gabesk/xmascard/hdl/test_individual_leds.v

`timescale 1ns / 1ps

//
// Validates that updating a pattern works according to design.
//


// In testing on the hardware, PuTTY was having trouble reliably sending and
// receiving the lowercase letter 'a'. Nothing else; the test data here worked
// fine. So this variation attempts to figure out why.
// Wait a random amount of time, then send 'a', repeatedly over and over. If the
// receiver ever receives something other than 'a' back, assert.

module test;

    // Inputs
    reg clk = 0;
    reg rx = 1; // RS-232 idle condition is logic high
    reg xmit = 0;
    reg recv = 0;
    reg write_complete_received = 0;
    reg test_step_complete = 0;

    integer i = 0;
    integer j = 0;
    integer random_delay;
    reg [7:0] received_byte = 0;

    reg [7:0] test_send_vector [0:576];
    integer test_send_vector_len = 576;
    reg [7:0] test_receive_vector [0:384];
    integer test_receive_vector_len = 384;
    
    initial begin
        test_send_vector[0]  = "i";
        test_send_vector[1]  = 8'h0;
        test_send_vector[2]  = 8'h0;
        test_send_vector[3]  = "i";
        test_send_vector[4]  = 8'h0;
        test_send_vector[5]  = 8'h1;
        test_send_vector[6]  = "i";
        test_send_vector[7]  = 8'h0;
        test_send_vector[8]  = 8'h2;
        test_send_vector[9]  = "i";
        test_send_vector[10]  = 8'h0;
        test_send_vector[11]  = 8'h3;
        test_send_vector[12]  = "i";
        test_send_vector[13]  = 8'h0;
        test_send_vector[14]  = 8'h4;
        test_send_vector[15]  = "i";
        test_send_vector[16]  = 8'h0;
        test_send_vector[17]  = 8'h5;
        test_send_vector[18]  = "i";
        test_send_vector[19]  = 8'h0;
        test_send_vector[20]  = 8'h6;
        test_send_vector[21]  = "i";
        test_send_vector[22]  = 8'h0;
        test_send_vector[23]  = 8'h7;
        test_send_vector[24]  = "i";
        test_send_vector[25]  = 8'h1;
        test_send_vector[26]  = 8'h0;
        test_send_vector[27]  = "i";
        test_send_vector[28]  = 8'h1;
        test_send_vector[29]  = 8'h1;
        test_send_vector[30]  = "i";
        test_send_vector[31]  = 8'h1;
        test_send_vector[32]  = 8'h2;
        test_send_vector[33]  = "i";
        test_send_vector[34]  = 8'h1;
        test_send_vector[35]  = 8'h3;
        test_send_vector[36]  = "i";
        test_send_vector[37]  = 8'h1;
        test_send_vector[38]  = 8'h4;
        test_send_vector[39]  = "i";
        test_send_vector[40]  = 8'h1;
        test_send_vector[41]  = 8'h5;
        test_send_vector[42]  = "i";
        test_send_vector[43]  = 8'h1;
        test_send_vector[44]  = 8'h6;
        test_send_vector[45]  = "i";
        test_send_vector[46]  = 8'h1;
        test_send_vector[47]  = 8'h7;
        test_send_vector[48]  = "i";
        test_send_vector[49]  = 8'h2;
        test_send_vector[50]  = 8'h0;
        test_send_vector[51]  = "i";
        test_send_vector[52]  = 8'h2;
        test_send_vector[53]  = 8'h1;
        test_send_vector[54]  = "i";
        test_send_vector[55]  = 8'h2;
        test_send_vector[56]  = 8'h2;
        test_send_vector[57]  = "i";
        test_send_vector[58]  = 8'h2;
        test_send_vector[59]  = 8'h3;
        test_send_vector[60]  = "i";
        test_send_vector[61]  = 8'h2;
        test_send_vector[62]  = 8'h4;
        test_send_vector[63]  = "i";
        test_send_vector[64]  = 8'h2;
        test_send_vector[65]  = 8'h5;
        test_send_vector[66]  = "i";
        test_send_vector[67]  = 8'h2;
        test_send_vector[68]  = 8'h6;
        test_send_vector[69]  = "i";
        test_send_vector[70]  = 8'h2;
        test_send_vector[71]  = 8'h7;
        test_send_vector[72]  = "i";
        test_send_vector[73]  = 8'h3;
        test_send_vector[74]  = 8'h0;
        test_send_vector[75]  = "i";
        test_send_vector[76]  = 8'h3;
        test_send_vector[77]  = 8'h1;
        test_send_vector[78]  = "i";
        test_send_vector[79]  = 8'h3;
        test_send_vector[80]  = 8'h2;
        test_send_vector[81]  = "i";
        test_send_vector[82]  = 8'h3;
        test_send_vector[83]  = 8'h3;
        test_send_vector[84]  = "i";
        test_send_vector[85]  = 8'h3;
        test_send_vector[86]  = 8'h4;
        test_send_vector[87]  = "i";
        test_send_vector[88]  = 8'h3;
        test_send_vector[89]  = 8'h5;
        test_send_vector[90]  = "i";
        test_send_vector[91]  = 8'h3;
        test_send_vector[92]  = 8'h6;
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
        test_receive_vector[364]  = 8'h16;
        test_receive_vector[365]  = 8'h6;
        test_receive_vector[366]  = 8'h16;
        test_receive_vector[367]  = 8'h7;
        test_receive_vector[368]  = 8'h17;
        test_receive_vector[369]  = 8'h0;
        test_receive_vector[370]  = 8'h17;
        test_receive_vector[371]  = 8'h1;
        test_receive_vector[372]  = 8'h17;
        test_receive_vector[373]  = 8'h2;
        test_receive_vector[374]  = 8'h17;
        test_receive_vector[375]  = 8'h3;
        test_receive_vector[376]  = 8'h17;
        test_receive_vector[377]  = 8'h4;
        test_receive_vector[378]  = 8'h17;
        test_receive_vector[379]  = 8'h5;
        test_receive_vector[380]  = 8'h17;
        test_receive_vector[381]  = 8'h6;
        test_receive_vector[382]  = 8'h17;
        test_receive_vector[383]  = 8'h7;
    end
    // Outputs
    wire tx;
    wire [23:0] leds;

    // Instantiate the Unit Under Test (UUT)
    lights uut (
        .clk(clk),
        .rx(rx),
        .tx(tx),
        .leds(leds)
    );

    always #20 clk = ~clk;

    // Transmission loop
    initial begin
        // Wait 100 ns for global reset to finish and a little longer for good measure.
        #100;
        #1234;

        for (i=0; i<test_send_vector_len; i=i+1) begin
            $display("Send i: %d val: %x", i, test_send_vector[i]);
            xmit_byte(test_send_vector[i]);
            if ((i+1) % 3 == 0) @ (test_step_complete) test_step_complete = 0; // Wait for module to echo result back to us
            // Wait random time
            random_delay = $random % 1000000; // Up to 1 ms
            #(random_delay);
        end

        #1000000
        if (write_complete_received == 0)   $display("Test failed");
        else                                $display("Test passed");
        $stop;
    end
    
    // Receiver loop
    always begin
        for (j=0; j<test_receive_vector_len; j=j+1) begin
            recv_byte(received_byte);
            $display("Recv j: %d expect: %x val: %x", j, test_receive_vector[j], received_byte);
            if (received_byte != test_receive_vector[j]) $stop;
            if ((j+1) % 2 == 0) test_step_complete = 1;
        end

        write_complete_received = 1;
    end

    task xmit_byte();
        input [7:0] b;
        integer i;
        begin
            #8681 rx = 0; xmit = 1; // start bit

            for (i=0;i<8;i = i+1) begin
                #8681 rx = b[0]; xmit = 0; // 0
                b = {1'b0, b[7:1]};
            end

            #8681 rx = 1; // stop bit
        end
    endtask
    
    task recv_byte();
        output [7:0] b;
        integer i;
        begin
            b = 0;
            @ (negedge tx); // Wait for start bit
            recv = 1;
            #4340;          // Wait half a bit period to align sampling to middle of transition.
            // 8 times, wait a bit period and then sample the value, shifting in from left to right.
            for (i=0;i<8;i = i+1) begin
                b = {1'b0, b[7:1]};
                #8681 b[7] = tx; recv = 0;
            end
            #4340;          // Wait another half a bit period to give the stop bit some time to occur.
        end
    endtask
    
endmodule
